srikit/ssd-clock-module/design/MCU-MASTER.sch

## KiCad design design/MCU-MASTER.sch (2021-03-07)

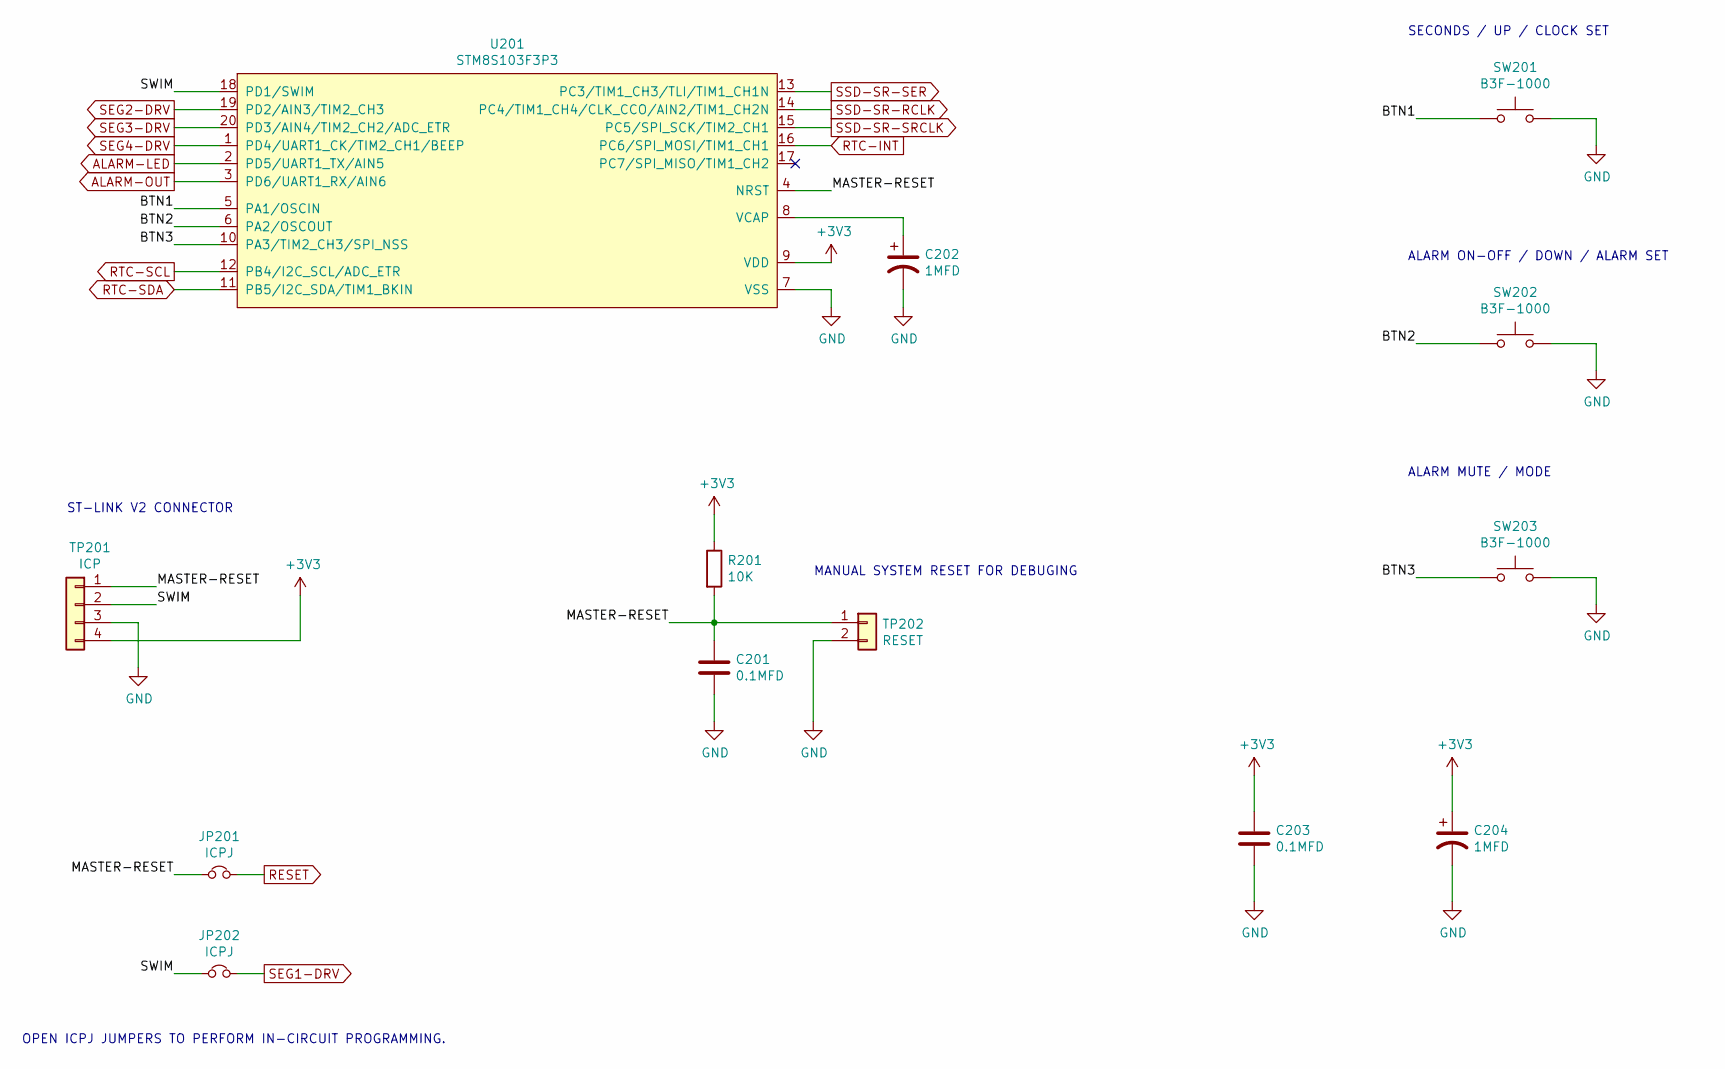
[picture p6: schematic MCU-MASTER.sch]

Parts:
C201, C203: 0.1MFD; C_0805_2012Metric_Pad1.15x1.40mm_HandSolder
C202: 1MFD; C_0805_2012Metric_Pad1.15x1.40mm_HandSolder
C204: 1MFD; CP_Radial_D5.0mm_P2.50mm
JP201, JP202: ICPJ; SolderJumper-2_P1.3mm_Bridged_Pad1.0x1.5mm
R201: 10K; R_0805_2012Metric_Pad1.15x1.40mm_HandSolder
SW201, SW202, SW203: B3F-1000; SW_PUSH_6mm
TP201: ICP; pogo-2.54mmx4
TP202: RESET; TestPoint-1.5mmx2
U201: STM8S103F3P3; TSSOP-20_4.4x6.5mm_P0.65mm

Connections:
+3V3: C203.1, C204.1, R201.1, TP201.4, U201.9 (VDD)
ALARM-LED: U201.2 (PD5/UART1_TX/AIN5)
ALARM-OUT: U201.3 (PD6/UART1_RX/AIN6)
BTN1: SW201.1, U201.5 (PA1/OSCIN)
BTN2: SW202.1, U201.6 (PA2/OSCOUT)
BTN3: SW203.1, U201.10 (PA3/TIM2_CH3/SPI_NSS)
GND: C201.2, C202.2, C203.2, C204.2, SW201.2, SW202.2, SW203.2, TP201.3, TP202.2, U201.7 (VSS)
MASTER-RESET: C201.1, JP201.1, R201.2, TP201.1, TP202.1, U201.4 (NRST)
unnamed: C202.1, U201.8 (VCAP)
RESET: JP201.2
RTC-INT: U201.16 (PC6/SPI_MOSI/TIM1_CH1)
RTC-SCL: U201.12 (PB4/I2C_SCL/ADC_ETR)
RTC-SDA: U201.11 (PB5/I2C_SDA/TIM1_BKIN)
SEG1-DRV: JP202.2
SEG2-DRV: U201.19 (PD2/AIN3/TIM2_CH3)
SEG3-DRV: U201.20 (PD3/AIN4/TIM2_CH2/ADC_ETR)
SEG4-DRV: U201.1 (PD4/UART1_CK/TIM2_CH1/BEEP)
SSD-SR-RCLK: U201.14 (PC4/TIM1_CH4/CLK_CCO/AIN2/TIM1_CH2N)
SSD-SR-SER: U201.13 (PC3/TIM1_CH3/TLI/TIM1_CH1N)
SSD-SR-SRCLK: U201.15 (PC5/SPI_SCK/TIM2_CH1)
SWIM: JP202.1, TP201.2, U201.18 (PD1/SWIM)

Notes on the sheet:
OPEN ICPJ JUMPERS TO PERFORM IN-CIRCUIT PROGRAMMING.
ST-LINK V2 CONNECTOR
MANUAL SYSTEM RESET FOR DEBUGING
SECONDS / UP / CLOCK SET
ALARM ON-OFF / DOWN / ALARM SET
ALARM MUTE / MODE
