srikit/ssd-clock-module/design/MPU-MASTER.sch

## KiCad design design/MPU-MASTER.sch (2021-03-05)

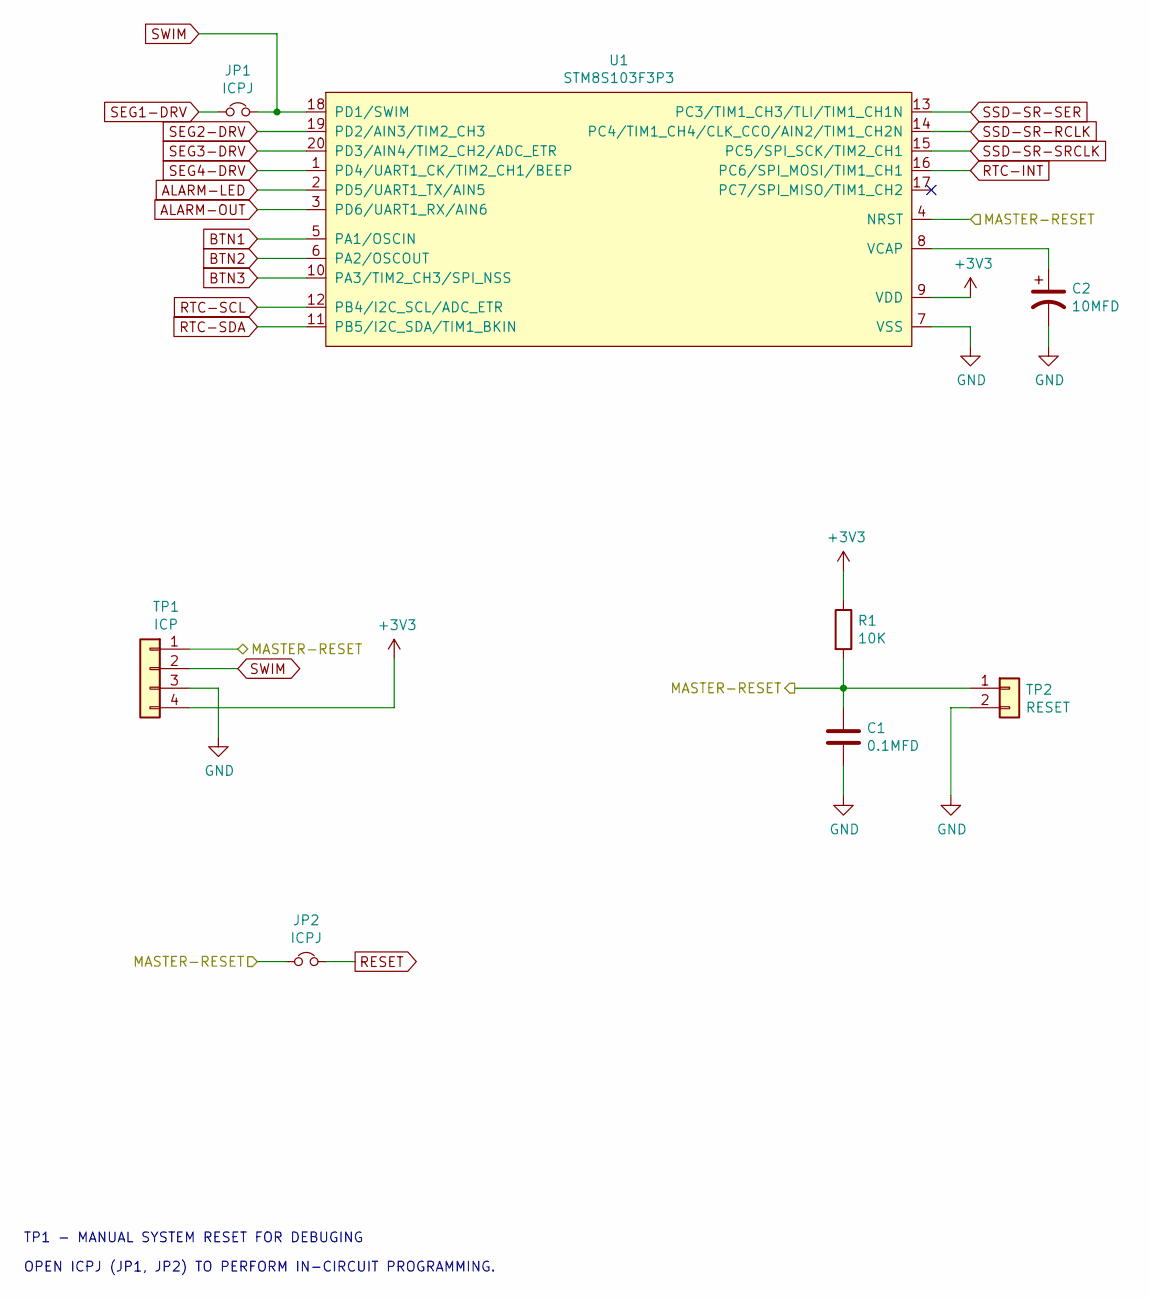
[picture p7: schematic MPU-MASTER.sch]

Parts:
C1: 0.1MFD
C2: 10MFD
JP1, JP2: ICPJ
R1: 10K
TP1: ICP
TP2: RESET
U1: STM8S103F3P3; TSSOP-20_4.4x6.5mm_P0.65mm

Connections:
+3V3: R1.1, TP1.4, U1.9 (VDD)
ALARM-LED: U1.2 (PD5/UART1_TX/AIN5)
ALARM-OUT: U1.3 (PD6/UART1_RX/AIN6)
BTN1: U1.5 (PA1/OSCIN)
BTN2: U1.6 (PA2/OSCOUT)
BTN3: U1.10 (PA3/TIM2_CH3/SPI_NSS)
GND: C1.2, C2.2, TP1.3, TP2.2, U1.7 (VSS)
MASTER-RESET: C1.1, JP2.1, R1.2, TP1.1, TP2.1, U1.4 (NRST)
unnamed: C2.1, U1.8 (VCAP)
RESET: JP2.2
RTC-INT: U1.16 (PC6/SPI_MOSI/TIM1_CH1)
RTC-SCL: U1.12 (PB4/I2C_SCL/ADC_ETR)
RTC-SDA: U1.11 (PB5/I2C_SDA/TIM1_BKIN)
SEG1-DRV: JP1.1
SEG2-DRV: U1.19 (PD2/AIN3/TIM2_CH3)
SEG3-DRV: U1.20 (PD3/AIN4/TIM2_CH2/ADC_ETR)
SEG4-DRV: U1.1 (PD4/UART1_CK/TIM2_CH1/BEEP)
SSD-SR-RCLK: U1.14 (PC4/TIM1_CH4/CLK_CCO/AIN2/TIM1_CH2N)
SSD-SR-SER: U1.13 (PC3/TIM1_CH3/TLI/TIM1_CH1N)
SSD-SR-SRCLK: U1.15 (PC5/SPI_SCK/TIM2_CH1)
SWIM: JP1.2, TP1.2, U1.18 (PD1/SWIM)

Notes on the sheet:
OPEN ICPJ (JP1, JP2) TO PERFORM IN-CIRCUIT PROGRAMMING.
TP1 - MANUAL SYSTEM RESET FOR DEBUGING
