srikit/ssd-clock-module/design/RTC-ALARM.sch

## KiCad design design/RTC-ALARM.sch (2021-03-07)

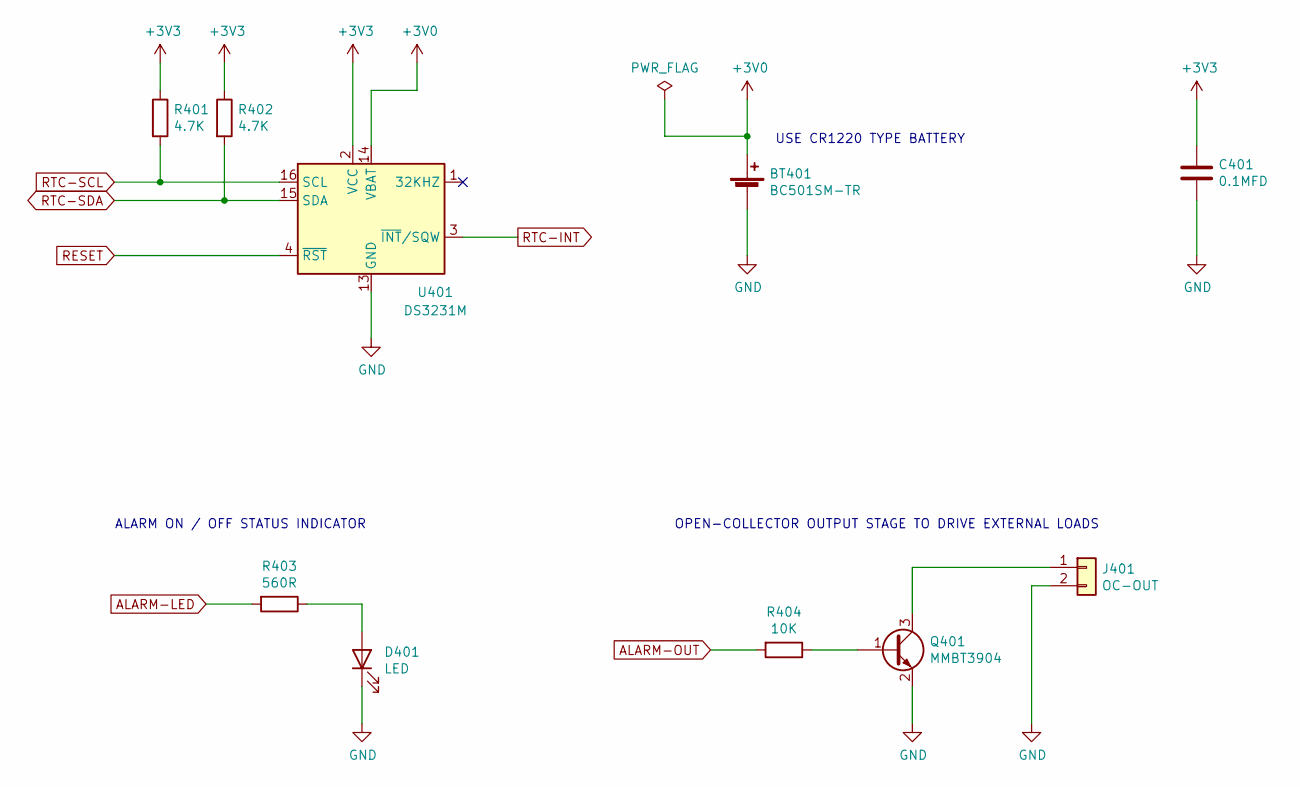
[picture p8: schematic RTC-ALARM.sch]

Parts:
BT401: BC501SM-TR; MPD_BC501SM-TR
C401: 0.1MFD; C_0805_2012Metric_Pad1.15x1.40mm_HandSolder
D401: LED; LED_D3.0mm
J401: OC-OUT; PinSocket_1x02_P2.54mm_Vertical
Q401: MMBT3904; SOT-23
R401, R402: 4.7K; R_0805_2012Metric_Pad1.15x1.40mm_HandSolder
R403: 560R; R_0805_2012Metric_Pad1.15x1.40mm_HandSolder
R404: 10K; R_0805_2012Metric_Pad1.15x1.40mm_HandSolder
U401: DS3231M; SOIC-16W_7.5x10.3mm_P1.27mm

Connections:
+3V0: BT401.1 (+), U401.14 (VBAT)
+3V3: C401.1, R401.1, R402.1, U401.2 (VCC)
ALARM-LED: R403.2
ALARM-OUT: R404.2
GND: BT401.2 (-), C401.2, D401.1 (K), J401.2, Q401.2 (E), U401.5 (GND), U401.6 (GND), U401.7 (GND), U401.8 (GND), U401.9 (GND), U401.10 (GND), U401.11 (GND), U401.12 (GND), U401.13 (GND)
unnamed: D401.2 (A), R403.1
unnamed: J401.1, Q401.3 (C)
unnamed: Q401.1 (B), R404.1
RESET: U401.4 (~RST)
RTC-INT: U401.3 (~INT~/SQW)
RTC-SCL: R401.2, U401.16 (SCL)
RTC-SDA: R402.2, U401.15 (SDA)

Notes on the sheet:
USE CR1220 TYPE BATTERY
OPEN-COLLECTOR OUTPUT STAGE TO DRIVE EXTERNAL LOADS
ALARM ON / OFF STATUS INDICATOR
