srikit/ssd-clock-module/design/SSD-DRIVER.sch

## KiCad design design/SSD-DRIVER.sch (2021-03-07)

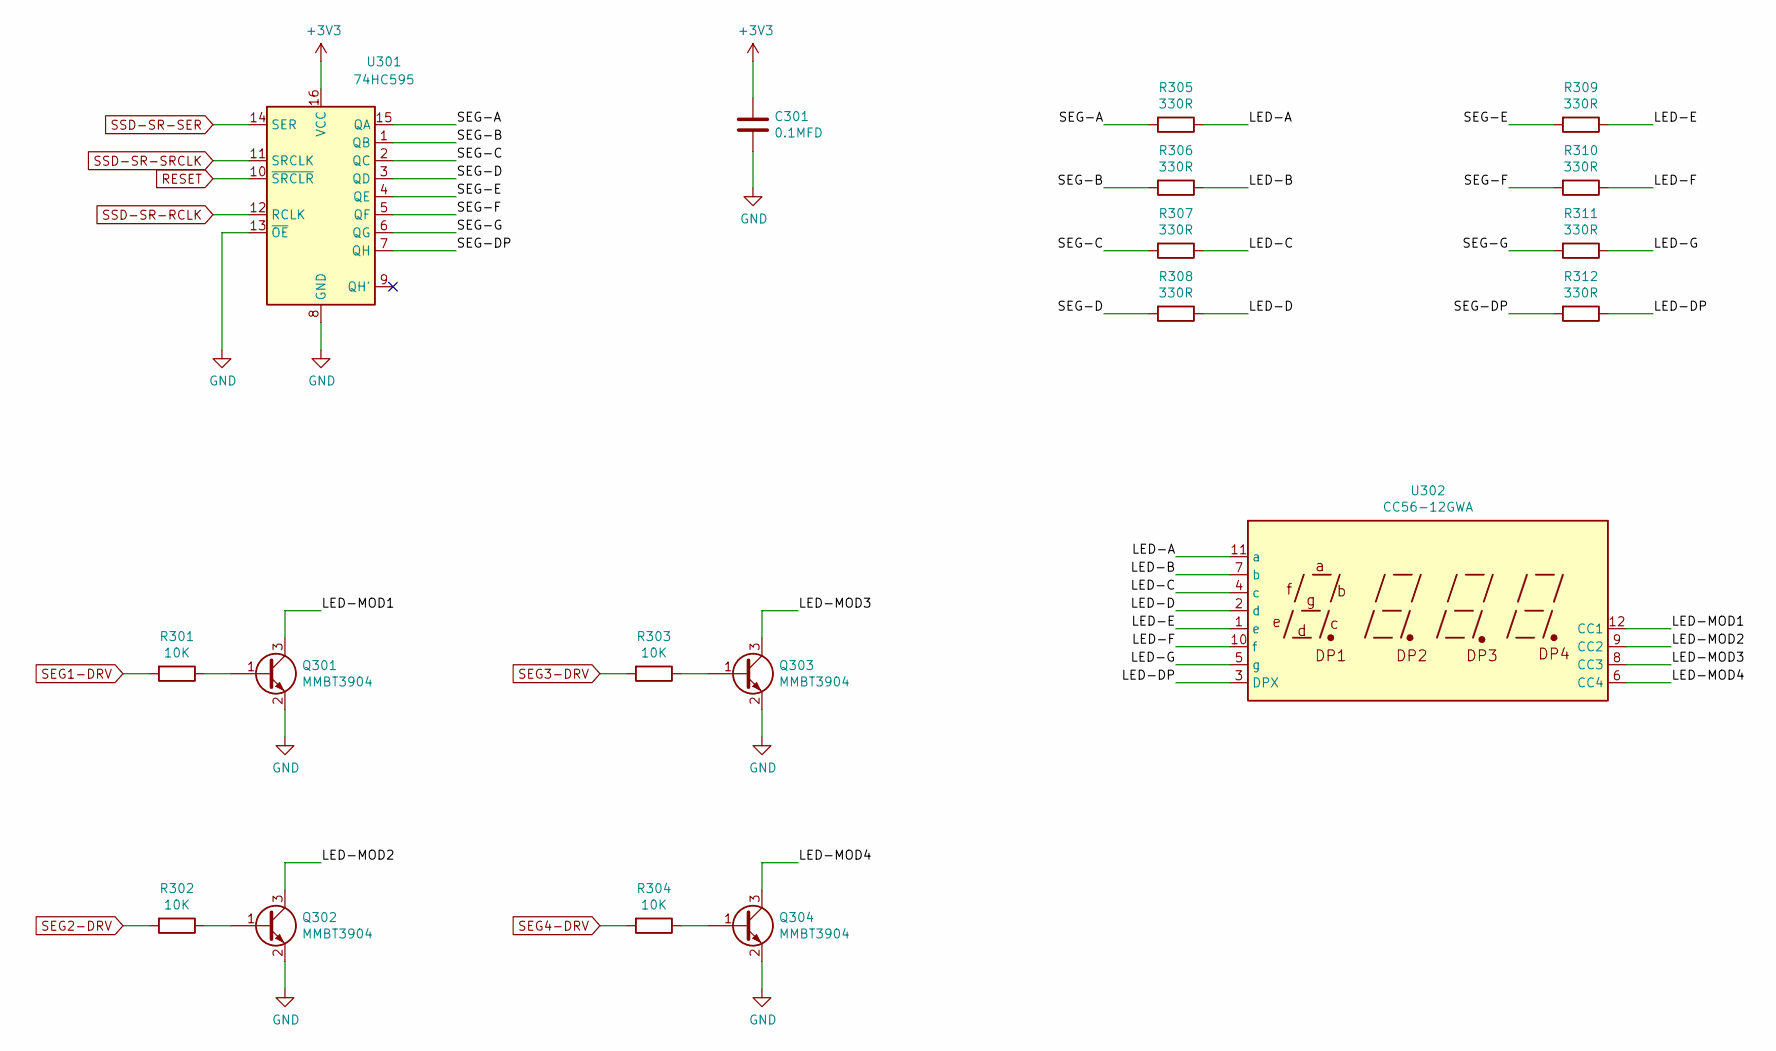
[picture p9: schematic SSD-DRIVER.sch]

Parts:
C301: 0.1MFD; C_0805_2012Metric_Pad1.15x1.40mm_HandSolder
Q301, Q302, Q303, Q304: MMBT3904; SOT-23
R301, R302, R303, R304: 10K; R_0805_2012Metric_Pad1.15x1.40mm_HandSolder
R305, R306, R307, R308, R309, R310, R311, R312: 330R; R_0805_2012Metric_Pad1.15x1.40mm_HandSolder
U301: 74HC595; SOP-16_4.4x10.4mm_P1.27mm
U302: CC56-12GWA

Connections:
+3V3: C301.1, U301.16 (VCC)
GND: C301.2, Q301.2 (E), Q302.2 (E), Q303.2 (E), Q304.2 (E), U301.8 (GND), U301.13 (~OE)
LED-A: R305.1, U302.11 (a)
LED-B: R306.1, U302.7 (b)
LED-C: R307.1, U302.4 (c)
LED-D: R308.1, U302.2 (d)
LED-DP: R312.1, U302.3 (DPX)
LED-E: R309.1, U302.1 (e)
LED-F: R310.1, U302.10 (f)
LED-G: R311.1, U302.5 (g)
LED-MOD1: Q301.3 (C), U302.12 (CC1)
LED-MOD2: Q302.3 (C), U302.9 (CC2)
LED-MOD3: Q303.3 (C), U302.8 (CC3)
LED-MOD4: Q304.3 (C), U302.6 (CC4)
unnamed: Q301.1 (B), R301.1
unnamed: Q302.1 (B), R302.1
unnamed: Q303.1 (B), R303.1
unnamed: Q304.1 (B), R304.1
RESET: U301.10 (~SRCLR)
SEG1-DRV: R301.2
SEG2-DRV: R302.2
SEG3-DRV: R303.2
SEG4-DRV: R304.2
SEG-A: R305.2, U301.15 (QA)
SEG-B: R306.2, U301.1 (QB)
SEG-C: R307.2, U301.2 (QC)
SEG-D: R308.2, U301.3 (QD)
SEG-DP: R312.2, U301.7 (QH)
SEG-E: R309.2, U301.4 (QE)
SEG-F: R310.2, U301.5 (QF)
SEG-G: R311.2, U301.6 (QG)
SSD-SR-RCLK: U301.12 (RCLK)
SSD-SR-SER: U301.14 (SER)
SSD-SR-SRCLK: U301.11 (SRCLK)
