srikit/ssd-clock-module/design/ssd-clock-module.sch

## KiCad design design/ssd-clock-module.sch (2021-03-07)

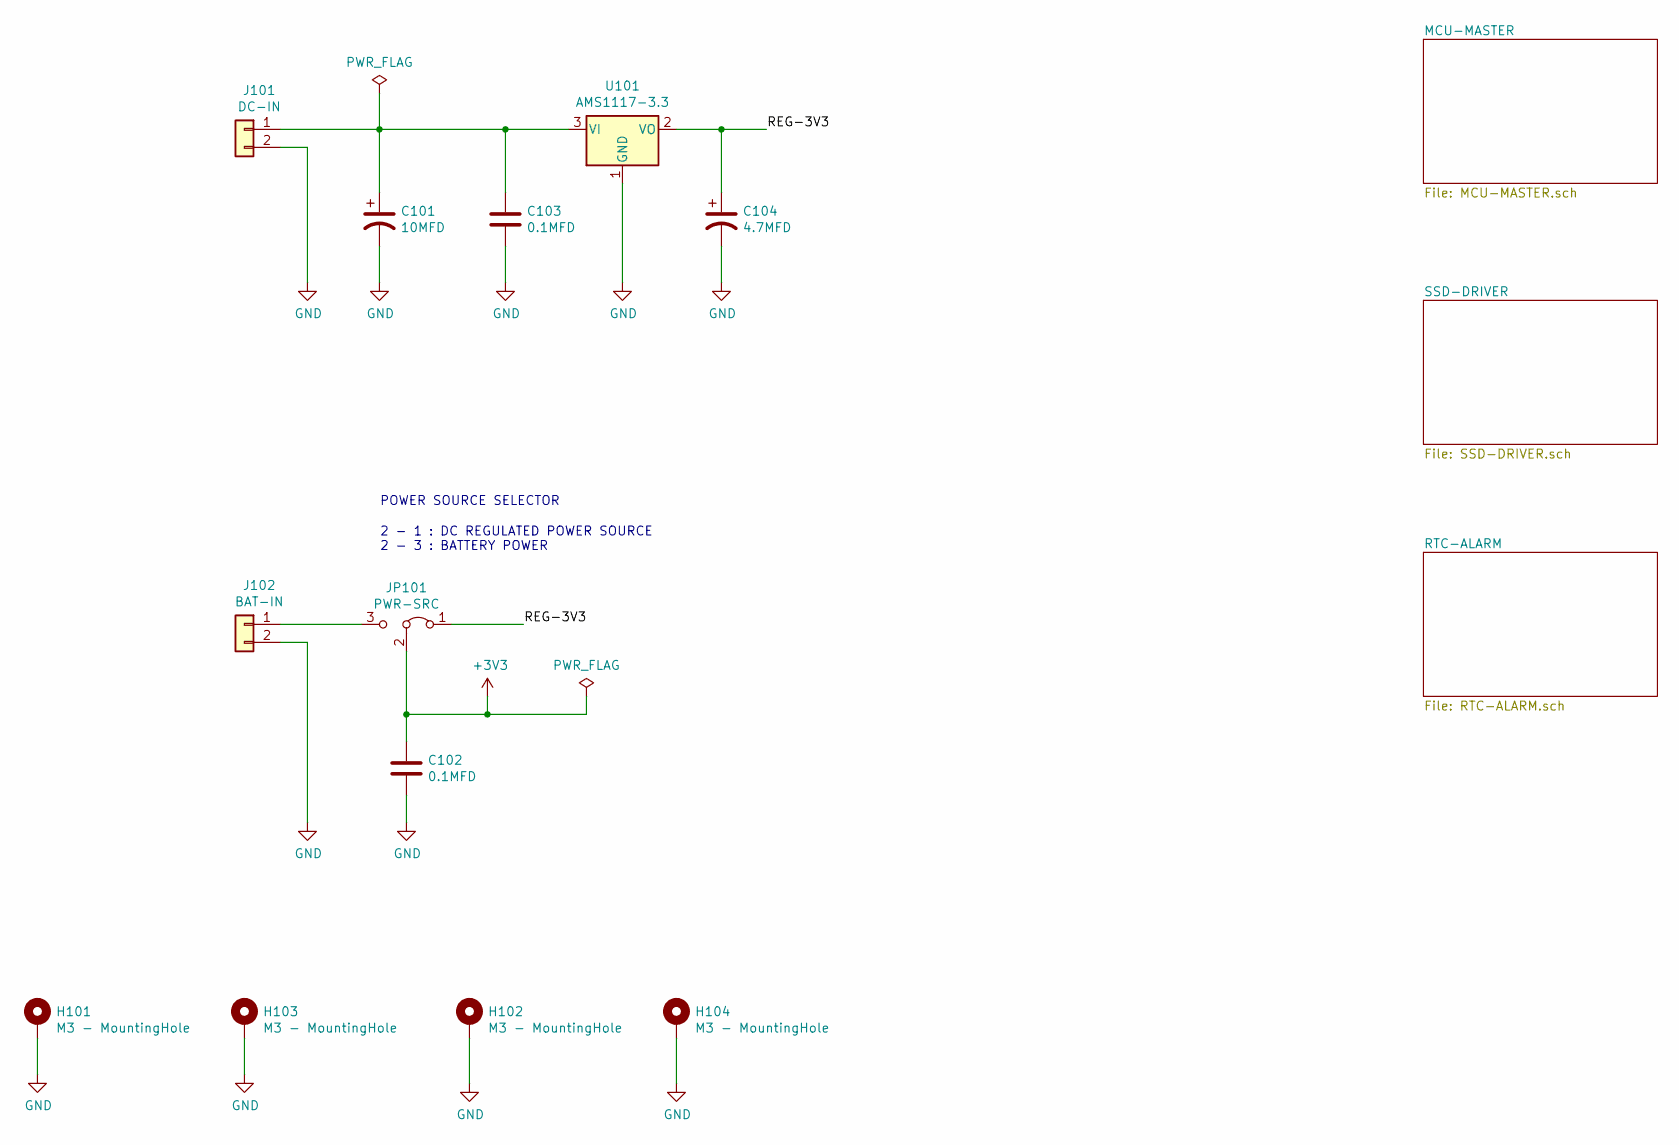
[picture p10: schematic ssd-clock-module.sch]

Parts:
C101: 10MFD; CP_Radial_D5.0mm_P2.50mm
C102, C103: 0.1MFD; C_0805_2012Metric_Pad1.15x1.40mm_HandSolder
C104: 4.7MFD; CP_Radial_D5.0mm_P2.50mm
H101, H102, H103, H104: M3 - MountingHole; MountingHole_3.2mm_M3_Pad
J101: DC-IN; PhoenixContact_MCV_1,5_2-G-3.5_1x02_P3.50mm_Vertical
J102: BAT-IN; SolderWire-0.75sqmm_1x02_P7mm_D1.25mm_OD3.5mm
JP101: PWR-SRC; PinSocket_1x03_P2.54mm_Vertical
U101: AMS1117-3.3; SOT-223-3_TabPin2

Connections:
+3V3: C102.1, JP101.2 (C)
GND: C101.2, C102.2, C103.2, C104.2, H101.1, H102.1, H103.1, H104.1, J101.2, J102.2, U101.1 (GND)
unnamed: C101.1, C103.1, J101.1, U101.3 (VI)
unnamed: J102.1, JP101.3 (B)
REG-3V3: C104.1, JP101.1 (A), U101.2 (VO)

Notes on the sheet:
POWER SOURCE SELECTOR
2 - 1 : DC REGULATED POWER SOURCE 2 - 3 : BATTERY POWER
